EcoApi/EcoApi_BeeHiveMonitoring/Hardware/images/EcoApi_pcb1.jpg

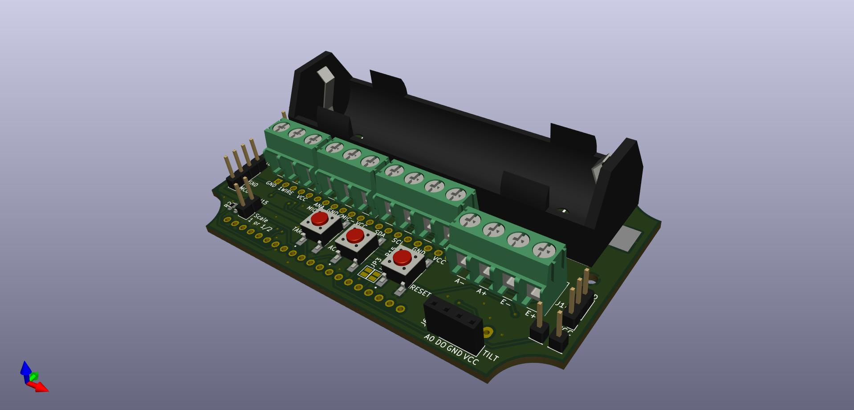
Hardware/images/EcoApi_pcb1.jpg
