EcoApi/EcoApi_BeeHiveMonitoring/Hardware/images/stm32_blue_black_pill_top.jpg

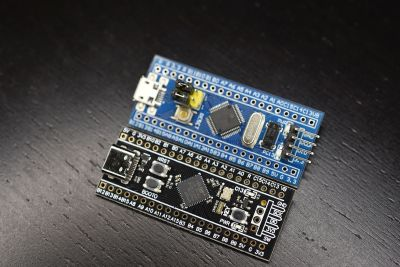
Hardware/images/stm32_blue_black_pill_top.jpg
