EcoApi/EcoApi_BeeHiveMonitoring/Hardware/lib_3d/MMBT4403_.step

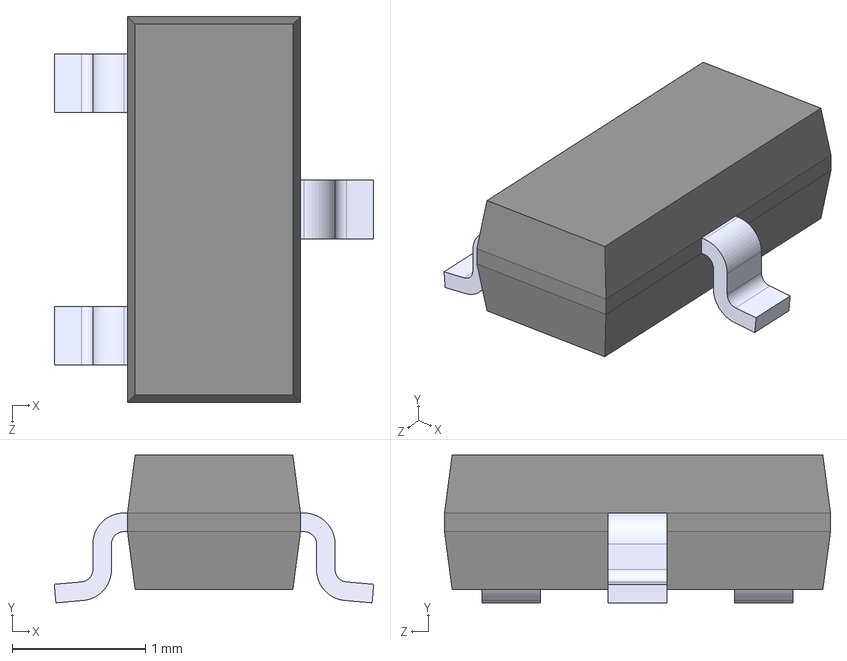
[picture p25: CAD file, 2022-01-26]
Hardware/lib_3d/MMBT4403_.step
2.40 x 1.11 x 2.90 mm
