EcoApi/EcoApi_BeeHiveMonitoring/Hardware/lib_3d/BLM18PG221SN1D.step

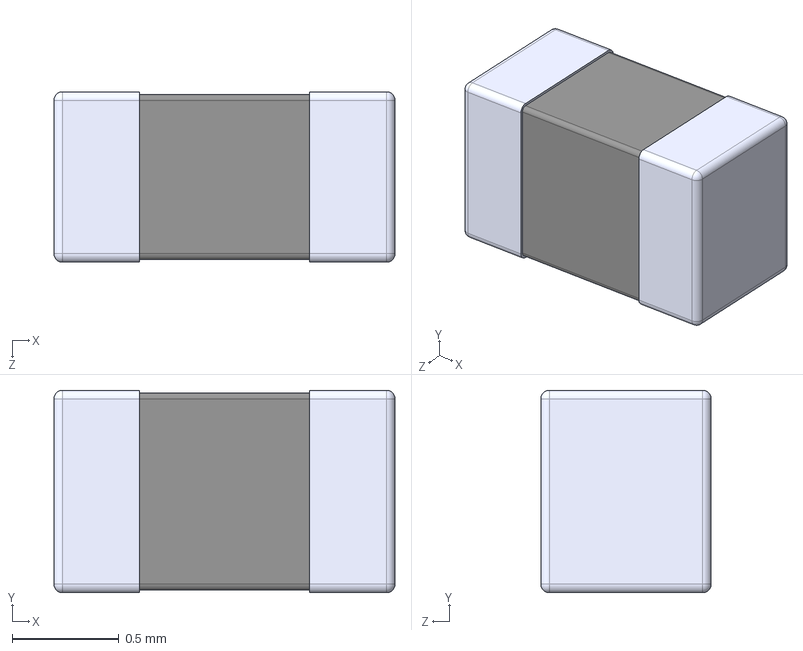
[picture p26: CAD file, 2022-01-07]
Hardware/lib_3d/BLM18PG221SN1D.step
1.60 x 0.95 x 0.8 mm
