EcoApi/EcoApi_BeeHiveMonitoring/Hardware/lib_3d/1042.step

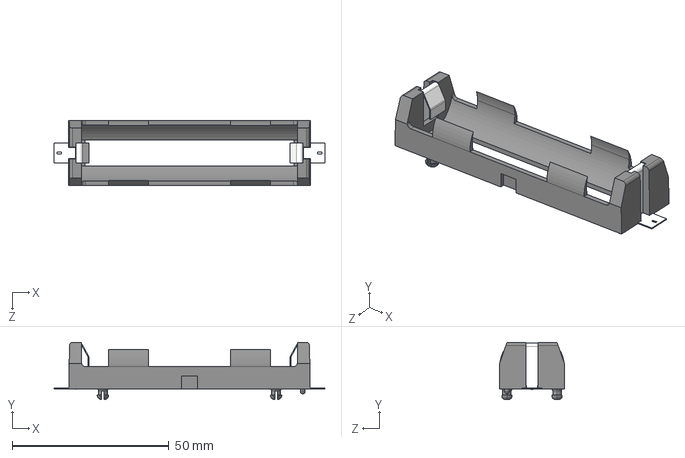
[picture p27: CAD file, 2022-01-07]
Hardware/lib_3d/1042.step
86.5 x 18.3 x 20.7 mm
