EcoApi/EcoApi_BeeHiveMonitoring/Hardware/lib_3d/TPL5010DDCR.step

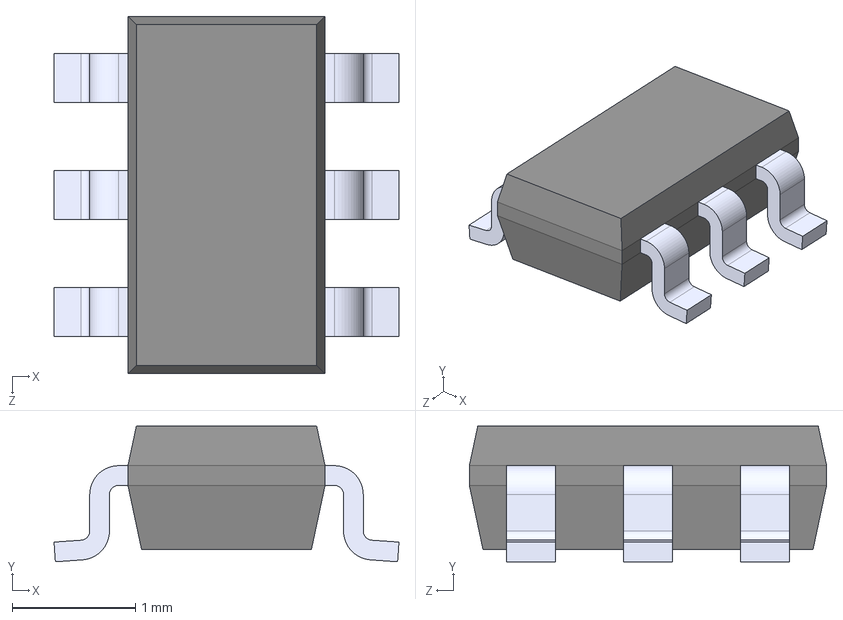
[picture p28: CAD file, 2022-01-07]
Hardware/lib_3d/TPL5010DDCR.step
2.80 x 1.10 x 2.90 mm
