EcoApi/EcoApi_BeeHiveMonitoring/Hardware/lib_3d/1N4148WT.step

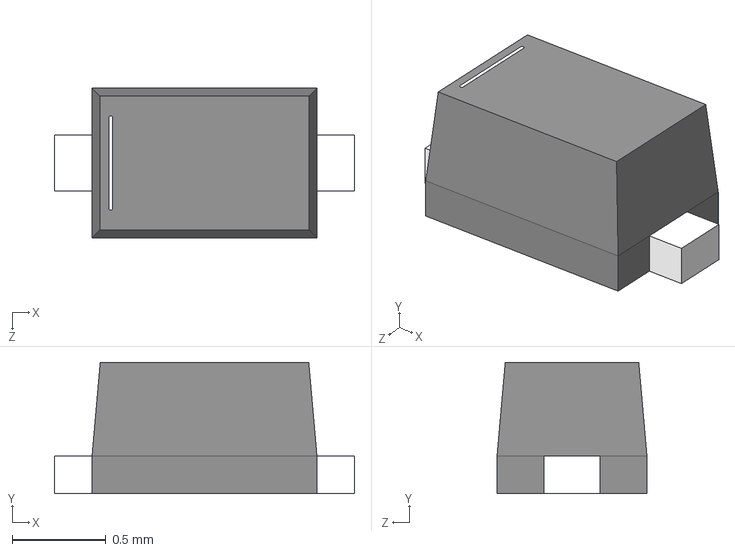
[picture p29: CAD file, 2022-01-07]
Hardware/lib_3d/1N4148WT.step
1.60 x 0.7 x 0.8 mm
