EcoApi/EcoApi_BeeHiveMonitoring/Hardware/lib_3d/B5B-XH-A__LF__SN_.stp

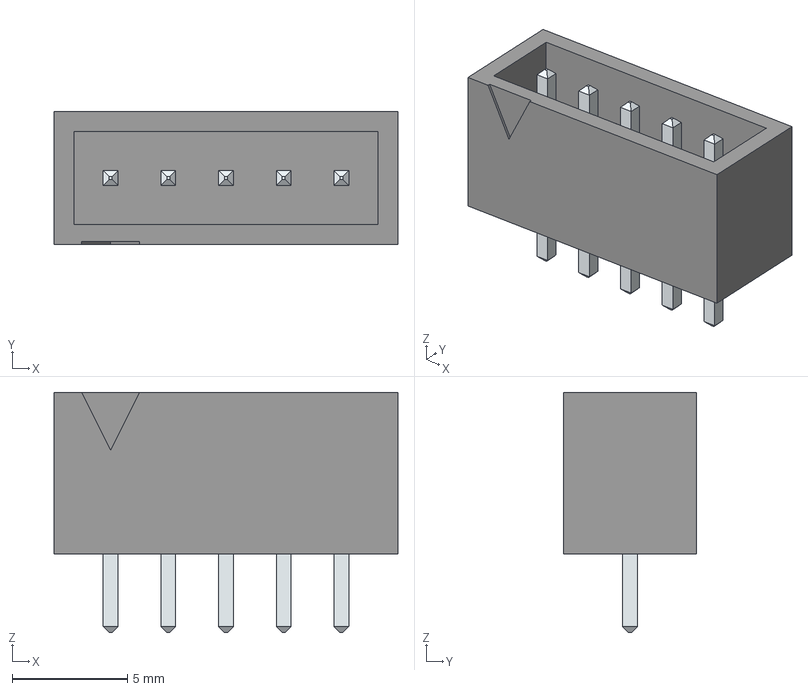
[picture p30: CAD file, 2022-01-07]
Hardware/lib_3d/B5B-XH-A__LF__SN_.stp
14.9 x 5.75 x 10.4 mm
LeadsArray
