EcoApi/EcoApi_BeeHiveMonitoring/Hardware/lib_3d/24LC02B_SN.step

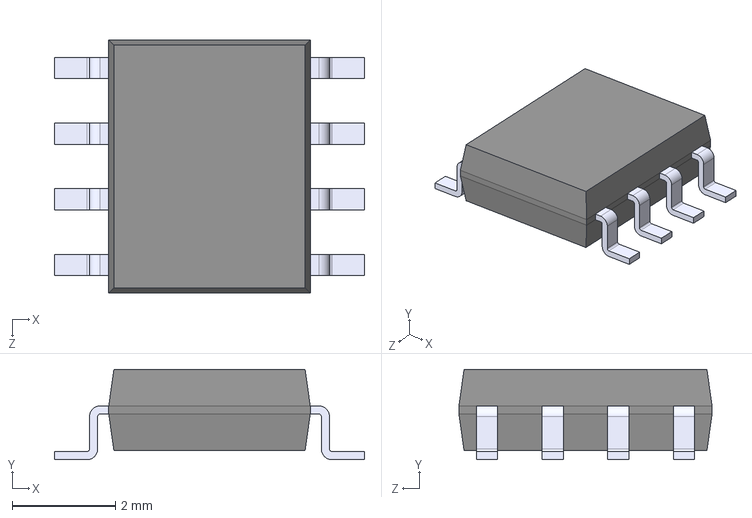
[picture p31: CAD file, 2022-01-07]
Hardware/lib_3d/24LC02B_SN.step
6.00 x 1.75 x 4.90 mm
