EcoApi/EcoApi_BeeHiveMonitoring/Hardware/lib_3d/Avia_Semiconductor_-_HX711.step

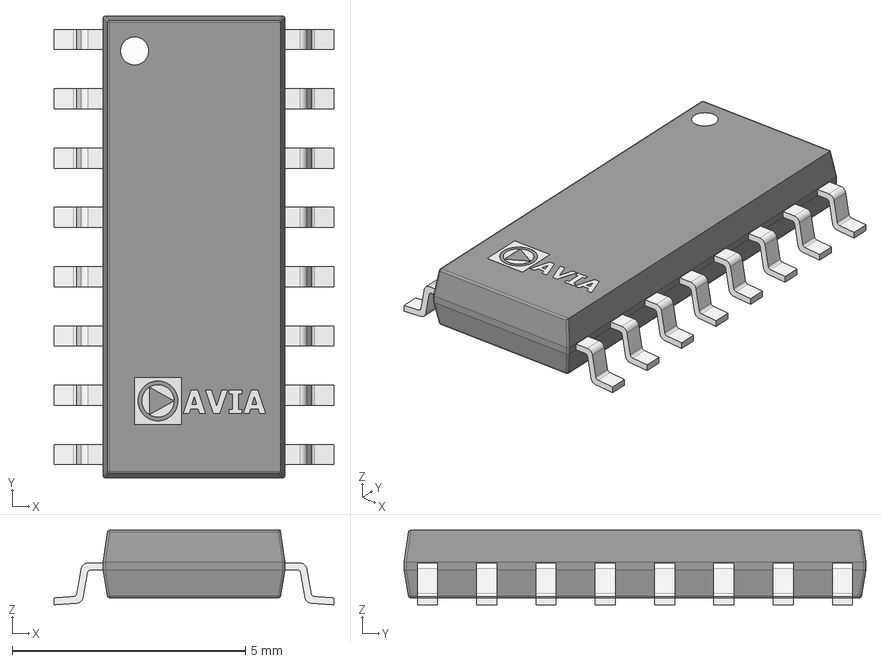
[picture p32: CAD file, 2022-01-07]
Hardware/lib_3d/Avia_Semiconductor_-_HX711.step
6.00 x 9.90 x 1.60 mm
IC_BODY
circle
IC_LEG x 8
IC_LEG_MIR7 x 8
AVIA
