EcoApi/EcoApi_BeeHiveMonitoring/Hardware/lib_3d/IRLML6246TRPBF.step

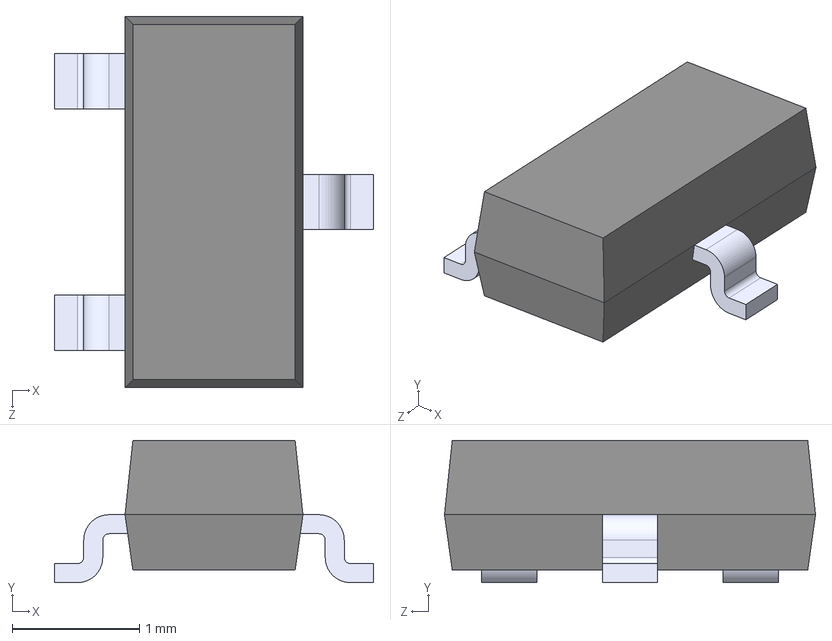
[picture p33: CAD file, 2022-01-07]
Hardware/lib_3d/IRLML6246TRPBF.step
2.51 x 1.12 x 2.92 mm
