EcoApi/EcoApi_BeeHiveMonitoring/Hardware/lib_3d/ON_Semiconductor_-_FDC638P.step

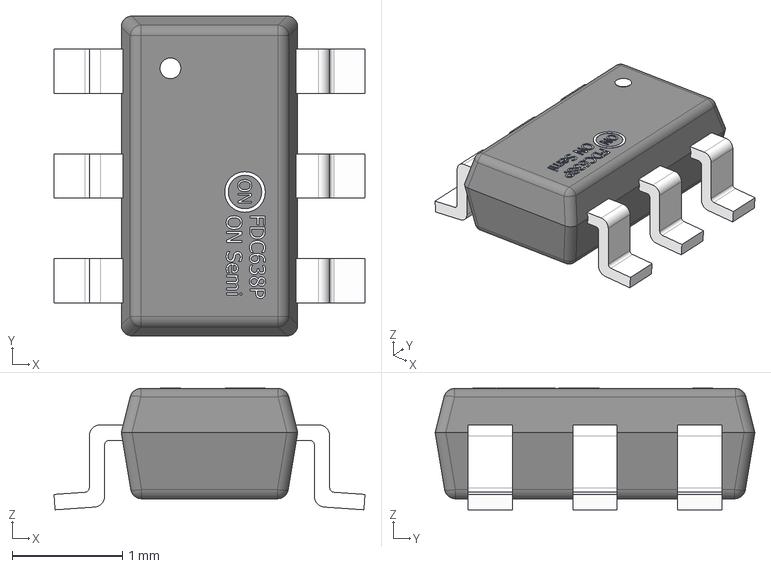
[picture p34: CAD file, 2022-01-07]
Hardware/lib_3d/ON_Semiconductor_-_FDC638P.step
2.82 x 2.90 x 1.10 mm
