EcoApi/EcoApi_BeeHiveMonitoring/Hardware/lib_3d/TP4056.step

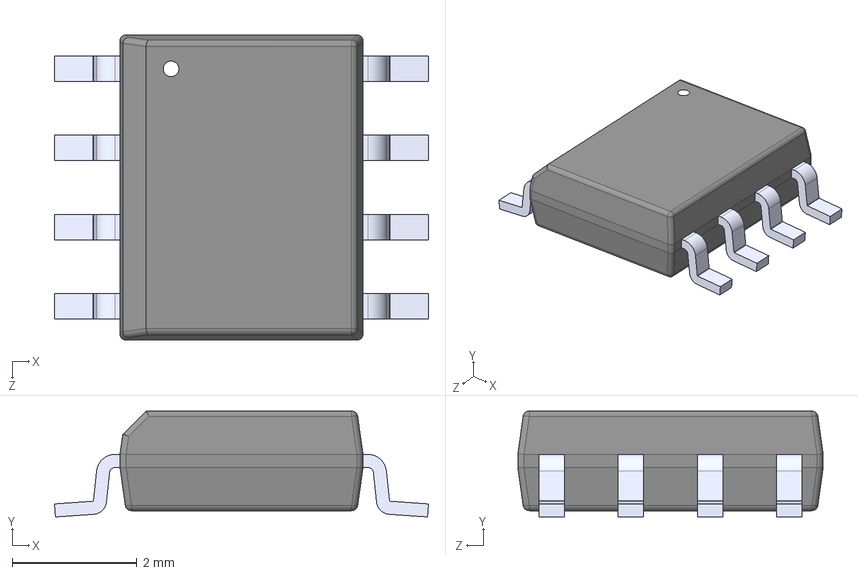
[picture p35: CAD file, 2022-01-07]
Hardware/lib_3d/TP4056.step
6.00 x 1.70 x 4.90 mm
