EcoApi/EcoApi_BeeHiveMonitoring/Hardware/lib_3d/B2B-XH-A.stp

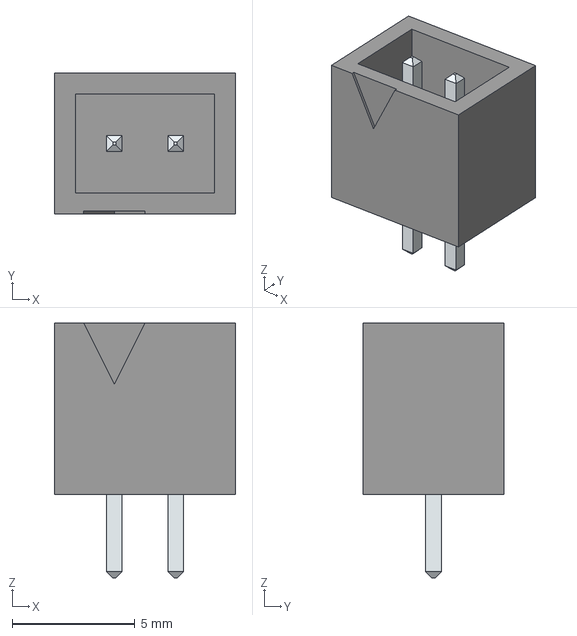
[picture p36: CAD file, 2022-01-07]
Hardware/lib_3d/B2B-XH-A.stp
7.40 x 5.75 x 10.4 mm
LeadsArray
