EcoApi/EcoApi_BeeHiveMonitoring/Hardware/lib_3d/MF-FSMF050X-2.step

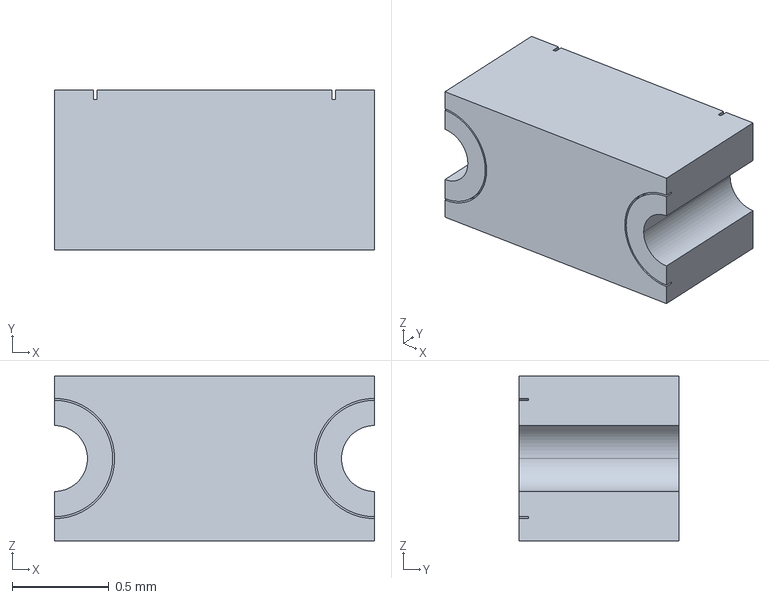
[picture p37: CAD file, 2022-01-07]
Hardware/lib_3d/MF-FSMF050X-2.step
1.65 x 0.825 x 0.85 mm
