EcoApi/EcoApi_BeeHiveMonitoring/Hardware/lib_3d/Fairchild_-_MMBT4403.step

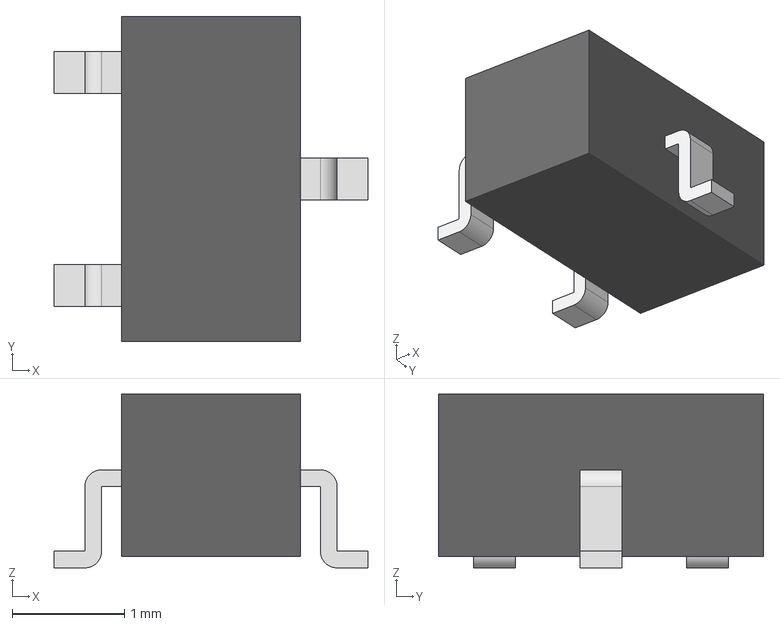
[picture p38: CAD file, 2022-01-07]
Hardware/lib_3d/Fairchild_-_MMBT4403.step
2.80 x 2.90 x 1.55 mm
