EcoApi/EcoApi_BeeHiveMonitoring/Hardware/lib_3d/UFQFPN-48_7X7X0P55MM.step

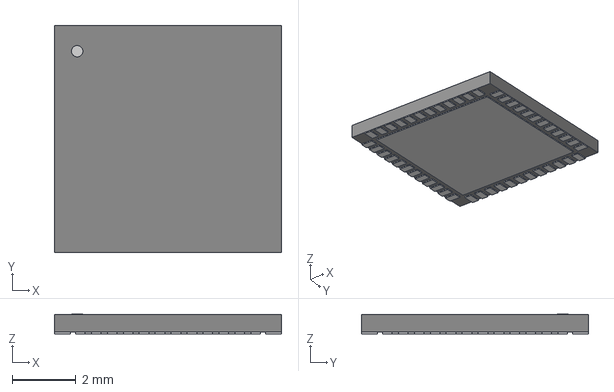
[picture p39: CAD file, 2022-01-07]
Hardware/lib_3d/UFQFPN-48_7X7X0P55MM.step
7.11 x 7.11 x 0.612 mm
