EcoApi/EcoApi_BeeHiveMonitoring/Hardware/lib_3d/B8B-XH-A_LF__SN_.stp

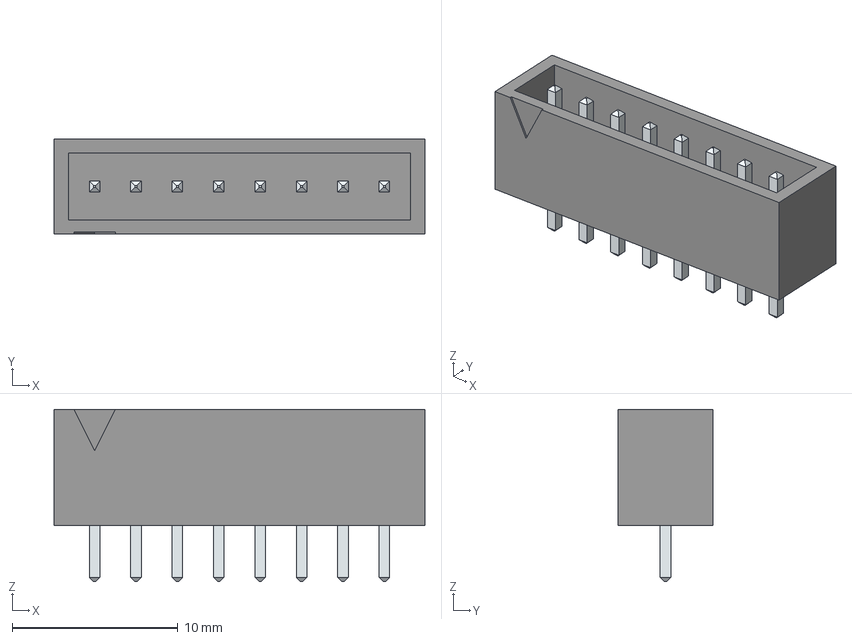
[picture p40: CAD file, 2022-01-07]
Hardware/lib_3d/B8B-XH-A_LF__SN_.stp
22.4 x 5.75 x 10.4 mm
LeadsArray
