EcoApi/EcoApi_BeeHiveMonitoring/Hardware/lib_3d/UCD0J102MNL1GS.stp

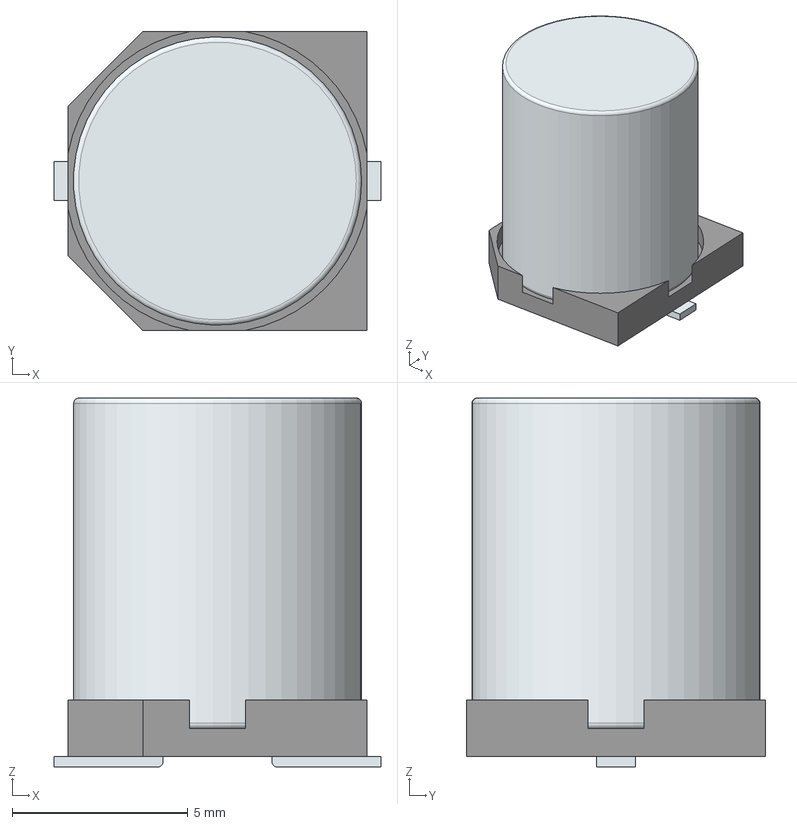
[picture p41: CAD file, 2021-04-09]
Hardware/lib_3d/UCD0J102MNL1GS.stp
9.30 x 8.50 x 10.5 mm
Base
Pin1Fillet
Pin2Fillet
