EcoApi/EcoApi_BeeHiveMonitoring/Hardware/lib_3d/EEE-FK0J102GP.stp

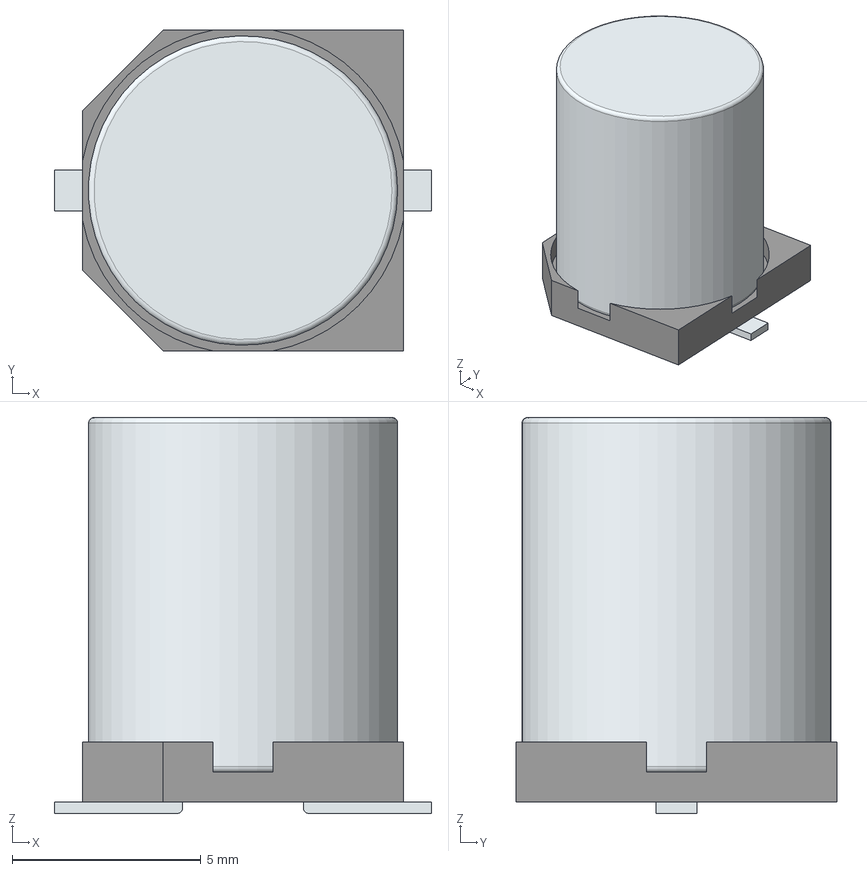
[picture p42: CAD file, 2021-04-09]
Hardware/lib_3d/EEE-FK0J102GP.stp
10.0 x 8.50 x 10.5 mm
Base
Pin1Fillet
Pin2Fillet
