EcoApi/EcoApi_BeeHiveMonitoring/Hardware/lib_3d/RFM9xW.step

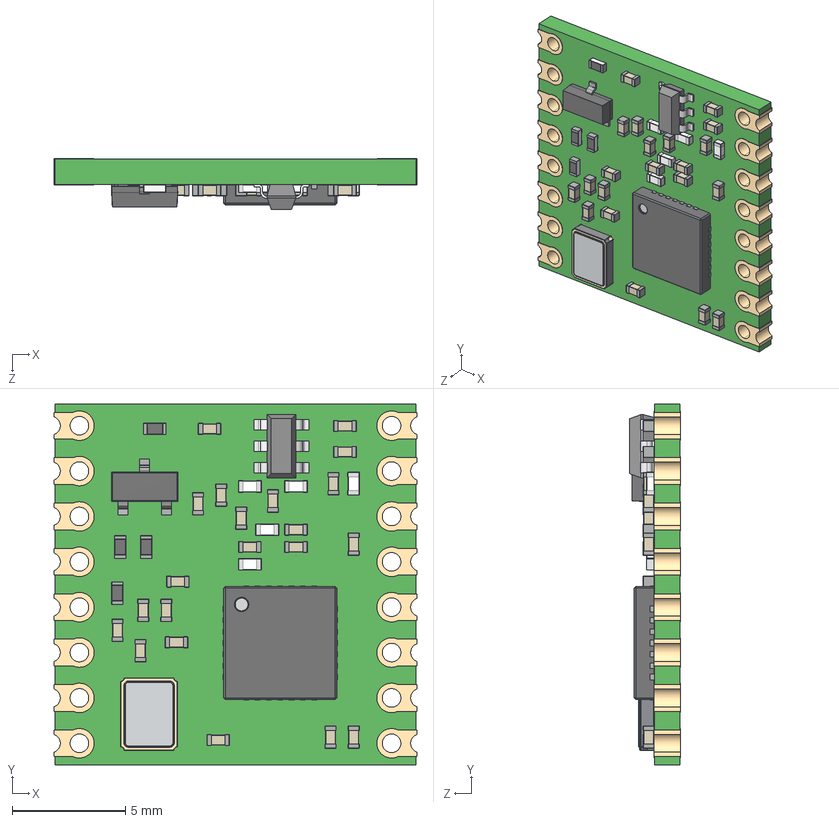
[picture p43: CAD file, 2021-04-09]
Hardware/lib_3d/RFM9xW.step
16.0 x 15.9 x 2.23 mm
Board
Cap0402 x 21
SW3dPS-inductor_0402_white x 5
SW3dPS-SOT-23-6
QFN28
TXC_7M
Res0402 x 4
User_Library-3-lead_sot23-3
Goldcontact x 16
