EcoApi/EcoApi_BeeHiveMonitoring/Hardware/lib_3d/HX711.STEP

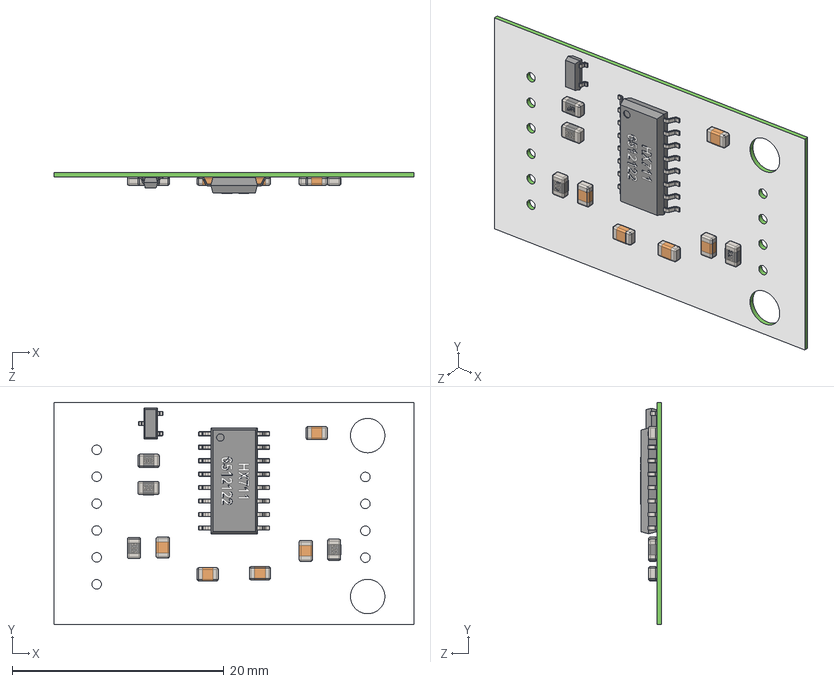
[picture p44: CAD file, 2021-04-09]
Hardware/lib_3d/HX711.STEP
34.0 x 21.0 x 1.97 mm
placa_Valor predeterminado
base_HX711_Valor predeterminado
pino_HX711_Valor predeterminado x 16
RESISTOR_SMD_122_Valor predeterminado x 2
RESISTOR_SMD_822_Valor predeterminado
RESISTOR_SMD_203_Valor predeterminado
CAPACITOR_805_Valor predeterminado x 5
TRANSISTOR_SOT23_Valor predeterminado
PINO_SOT23_Valor predeterminado x 3
