EcoApi/EcoApi_BeeHiveMonitoring/Hardware/lib_3d/U.FL-R-SMT_01_.step

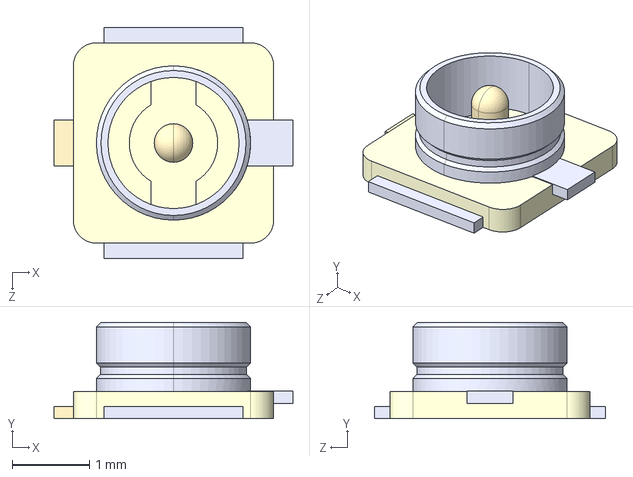
[picture p45: CAD file, 2021-04-09]
Hardware/lib_3d/U.FL-R-SMT_01_.step
3.10 x 1.25 x 3.00 mm
