EcoApi/EcoApi_BeeHiveMonitoring/Hardware/LTSpice/Draft3.asc

D1: diode; 1N4148
M1: pmos; FDC638P
M2: nmos; IRLML6244
M3: nmos; BSS123
R1: res; 2Meg; tol=1 pwr=0.1
R2: res; 100K; tol=1 pwr=0.1
R3: res; 2Meg; tol=1 pwr=0.1
R5: res; 1Meg; tol=1 pwr=0.1
V1: voltage; 4.2
V2: voltage; PULSE(4.2 0 2 0 0 0.1)
V3: voltage; PULSE(0 3.3 6 0 0 0.1)
Named nets: 0, VCC, UC, EN, PILE
.tran 10
