EcoApi/EcoApi_BeeHiveMonitoring/Hardware/LTSpice/Draft_diodeEn3v3.asc

D1: diode; 1N4148
D2: diode; 1N4148
D3: diode; 1N4148
R1: res; 1Meg; tol=1 pwr=0.1
V1: voltage; PULSE(3.3 0 1 0 0 1)
V2: voltage; PULSE(3.3 0 3 0 0 1)
V3: voltage; PULSE(3.3 0 5 0 0 1)
V4: voltage; 3.3
Named nets: VCC, OUT, S1, S2, S3, 0
.tran 9
