EcoApi/EcoApi_BeeHiveMonitoring/Hardware/LTSpice/Draft_inverter_wkup.asc

M3: nmos; BSS123
R3: res; 2Meg; tol=1 pwr=0.1
V1: voltage; 4.2
V3: voltage; PULSE(4.2 0 6 0 0 0.1)
Named nets: 0, VCC, RTC, PILE, OUT
.tran 10
