EcoApi/EcoApi_BeeHiveMonitoring/Hardware/LTSpice/Draft_tilt.asc

C1: cap; 0.1µF; V=6.3 Irms=2.55 Rser=0.0464862 Lser=0
R1: res; 1Meg; tol=1 pwr=0.1
S1: sw
V4: voltage; 4.2
V5: voltage; PULSE(0 4.2 0.1 0 0 0 0.001 10)
Named nets: VCC, OUT, 0
.tran 2
.model sw SW(Ron=0.1 Roff=1GIG Vt=2)
