EcoApi/EcoApi_BeeHiveMonitoring/Hardware/LTSpice/Draft_vbatt.asc

C1: cap; 0.01µ; V=10 Irms=0 Rser=0 Lser=0 mfg="Murata" pn="GCM033R71A103KA03" type="X7R"
M1: pmos; FDC638P
M2: nmos; IRLML6244
R1: res; 1Meg; tol=1 pwr=0.1
R2: res; 1Meg; tol=1 pwr=0.1
R3: res; 1Meg; tol=1 pwr=0.1
R5: res; 100K; tol=1 pwr=0.1
V1: voltage; 4.2
V3: voltage; PULSE(0 3.1 2 0 0 1)
Named nets: 0, UC, PILE, measure
.tran 10
