EcoApi/EcoApi_BeeHiveMonitoring/Software/src/board.h

/************************************************************************************//**
 *
 *	\file		board.h
 *
 *	\brief
 *
 *	\date		2 nov. 2021
 *
 *	\author		ecoapi
 *
 ***************************************************************************************/

#ifndef __BOARD_H_
#define __BOARD_H_

/***************************************************************************************/
/*	Includes																		
/***************************************************************************************/
#include <Arduino.h>

#ifdef __cplusplus
extern "C" {
#endif

#if defined(STM32F411xE) //blackpill
    #include "stm32f4xx_hal_rcc.h"
    #include "stm32f4xx_hal_adc.h"
    //#include "stm32f4xx_ll_adc.h"
#elif defined(STM32F103xB) //bluepill 
    #include "stm32f1xx_hal_rcc.h"
    #include "stm32f1xx_hal_adc.h"
    //#include "stm32f1xx_ll_adc.h"
#else
    #error "Bad µC defined"
#endif

#include "stm32yyxx_ll_adc.h"

/***************************************************************************************/
/* Define
/***************************************************************************************/
#define PACK( __Declaration__ ) __Declaration__ __attribute__((__packed__))

/*
-O0 : optimize for compile time and debug-ability. Most performance optimizations are disabled. This is the default for GCC.
-O1: pick the low hanging fruit in terms of performance, without impacting compilation time too much.
-O2: optimize for performance more aggressively, but not at the cost of larger code size.
-O3: optimize for performance at all cost, no matter the code size or compilation time impact.
-Ofast a.k.a. ludicrous mode: take off the guard rails, and disregard strict C standard compliance in the name of speed. This may lead to invalid programs.
-Os optimize for code size. This uses O2 as the baseline, but disables some optimizations. For example, it will not inline3 code if that leads to a size increase.

or

#pragma GCC push_options
#pragma GCC optimize ("O3")

 Code that needs optimizing

#pragma GCC pop_options
*/

//#define WEAK __attribute__ ((weak))

#define TRUE (1)
#define FALSE !(TRUE)

#define OK (0)
#define ERROR (-1)
#define DATA_NOT_CHANGED (ERROR - 1)

#define HX711_RATE PB5
#define HX711_DT PB6
#define HX711_CK PB7

#define SPI1_MOSI PA7
#define SPI1_MISO PA6
#define SPI1_SCK PA5
//#define SPI1_NSS PA_15
#define FLASH_NSS PA3
#define LORA_NSS PA4
#define LORA_RST PB0
#define LORA_DIO0 PB1
#define LORA_DIO1 PB2
#define LORA_DIO2 PB10
//#define LORA_DIO3 30//PB_15

#define UART1_TX PA9
#define UART1_RX PA10

#define PWR_OFF PA15

#define LED_INFO PA8
#define LED_BUITIN LED_INFO


#define WAKEUP_PIN PWR_WAKEUP_PIN1
#define WAKEUP PA0

//#define BTN_RST ?
//#define ONEWIRE_DATA PA_7
//#define ANA_VBATT PB_0
#define SCALE_TYPE PB15

#define BTN_TARE PA2
#define EN_VBATT BTN_TARE

#define TRACE_EN PB14
//#define BTN_ACT PA_4
//#define RING PA_1 //SYS_WKUP1

#define WDG_RELOAD PC13

#define MIC_ANA PA1
#define MIC_GAIN PB13

#define I2S_SD MIC_ANA
#define I2S_CK MIC_GAIN
#define I2S_WS PB12

#define I2C1_SCL PB8
#define I2C1_SDA PB9


#define EN_3V3_INT PB3
#define EN_3V3_EXT PB4

#ifdef __cplusplus
}
#endif
#endif
