EcoApi/EcoApi_BeeHiveMonitoring/Software/src/adc.h

/************************************************************************************//**
 *
 *	\file		adc.h
 *
 *	\brief
 *
 *	\date		2 nov. 2021
 *
 *	\author		ecoapi
 *
 ***************************************************************************************/

#ifndef __ADC_H
#define __ADC_H

/***************************************************************************************/
/*	Includes																		
/***************************************************************************************/
#include "board.h"

#ifdef __cplusplus
extern "C" {
#endif

/***************************************************************************************/
/* Define
/***************************************************************************************/

/***************************************************************************************/
/* Typedef                                                                        
/***************************************************************************************/
typedef enum Pin_ADC_ {
#if defined(STM32F411xE) //blackpill
    EXTERNAL_MIC = 1, //ADC1_IN1 -> MIC_ANA
#else
    #error "Bad µC defined"
#endif
    INTERNAL_TEMP = 32,
    INTERNAL_VREF,
    INTERNAL_VBAT,   

    Pin_ADC_MAX
} Pin_ADC;

/***************************************************************************************/
/*	Shared Functions																  
/***************************************************************************************/  
uint16_t AnalogRead(Pin_ADC pin);

#ifdef __cplusplus
}
#endif
#endif 
