EcoApi/EcoApi_BeeHiveMonitoring/Software/src/hx711.h

/************************************************************************************//**
 *
 *	\file		hx711.h
 *
 *	\brief
 *
 *	\date		2 nov. 2021
 *
 *	\author		ecoapi
 *
 ***************************************************************************************/

#ifndef __HX711_H_
#define __HX711_H_

/***************************************************************************************/
/*	Includes																		
/***************************************************************************************/
#include "board.h"
#if (USE_EEPROM == 1)
#include "eeprom.h"
#endif
#include "ramret.h"

#ifdef __cplusplus
extern "C" {
#endif

/***************************************************************************************/
/* Define
/***************************************************************************************/

/***************************************************************************************/
/* Typedef                                                                        
/***************************************************************************************/

/***************************************************************************************/
/*	Shared Functions																  
/***************************************************************************************/  
#if (USE_EEPROM == 1)
int32_t hx711_setup(t_Eeprom *pt_eeprom, t_RamRet *pt_ramRet);
#else
int32_t hx711_setup(t_RamRet *pt_eeprom, t_RamRet *pt_ramRet);
#endif
int32_t hx711_getData(t_telemetryData *pt_telemetryData);
int32_t hx711_suspend(void);

#ifdef __cplusplus
}
#endif
#endif
