EcoApi/EcoApi_BeeHiveMonitoring/Software/src/analog.h

/************************************************************************************//**
 *
 *	\file		analog.h
 *
 *	\brief
 *
 *	\date		2 nov. 2021
 *
 *	\author		ecoapi
 *
 ***************************************************************************************/
#ifndef __ANALOG_H_
#define __ANALOG_H_

/***************************************************************************************/
/*	Includes																		
/***************************************************************************************/
#include "board.h"
#include "ramret.h"

#ifdef __cplusplus
extern "C" {
#endif

/***************************************************************************************/
/* Define
/***************************************************************************************/

/***************************************************************************************/
/* Typedef                                                                        
/***************************************************************************************/

/***************************************************************************************/
/*	Shared Functions																  
/***************************************************************************************/  
float analog_getVBattPercent(int32_t vbatt);
int32_t analog_setup(t_RamRet *pt_ramRet, int32_t vRef);
int32_t analog_getData(t_telemetryData *pt_telemetryData);
int32_t analog_suspend(void);
int32_t analog_getInternalVref(void);

#ifdef __cplusplus
}
#endif
#endif
