EcoApi/EcoApi_BeeHiveMonitoring/Software/src/sht3x.h

/************************************************************************************//**
 *
 *	\file		sht3x.h
 *
 *	\brief
 *
 *	\date		2 nov. 2021
 *
 *	\author		ecoapi
 *
 ***************************************************************************************/

#ifndef __SHT3X_H_
#define __SHT3X_H_

/***************************************************************************************/
/*	Includes																		
/***************************************************************************************/
#include "board.h"
#include "ramret.h"

#ifdef __cplusplus
extern "C" {
#endif

/***************************************************************************************/
/* Define
/***************************************************************************************/

/***************************************************************************************/
/* Typedef                                                                        
/***************************************************************************************/

/***************************************************************************************/
/*	Shared Functions																  
/***************************************************************************************/  
int32_t sht3x_setup(t_RamRet *pt_ramRet);
int32_t sht3x_getData(t_telemetryData *pt_telemetryData);
int32_t sht3x_suspend(void);

#ifdef __cplusplus
}
#endif
#endif
