EcoApi/EcoApi_BeeHiveMonitoring/Software/src/bmp180.h

/************************************************************************************//**
 *
 *	\file		bmp180.h
 *
 *	\brief
 *
 *	\date		2 nov. 2021
 *
 *	\author		ecoapi
 *
 ***************************************************************************************/

#ifndef __BMP180_H_
#define __BMP180_H_

/***************************************************************************************/
/*	Includes																		
/***************************************************************************************/
#include "board.h"
#include "ramret.h"

#ifdef __cplusplus
extern "C" {
#endif

/***************************************************************************************/
/* Define
/***************************************************************************************/

/***************************************************************************************/
/* Typedef                                                                        
/***************************************************************************************/

/***************************************************************************************/
/*	Shared Functions																  
/***************************************************************************************/  
int32_t bmp180_setup(t_RamRet *pt_ramRet);
int32_t bmp180_getData(t_telemetryData *pt_telemetryData);
int32_t bmp180_suspend(void);

#ifdef __cplusplus
}
#endif
#endif
